goran-mahovlic/ulx3s-extensions/pic/GPDI_Back.png

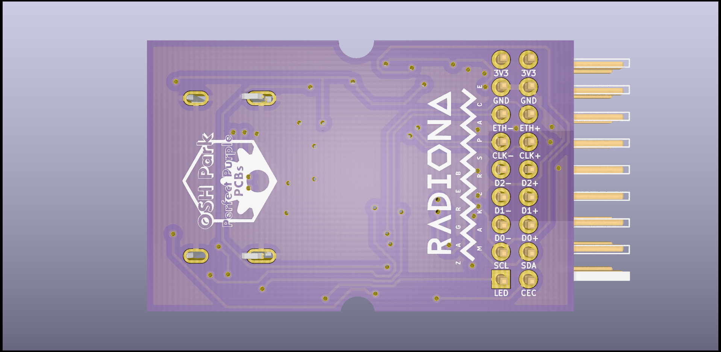
pic/GPDI_Back.png
