goran-mahovlic/ulx3s-extensions/pic/GPDI_INPUT.png

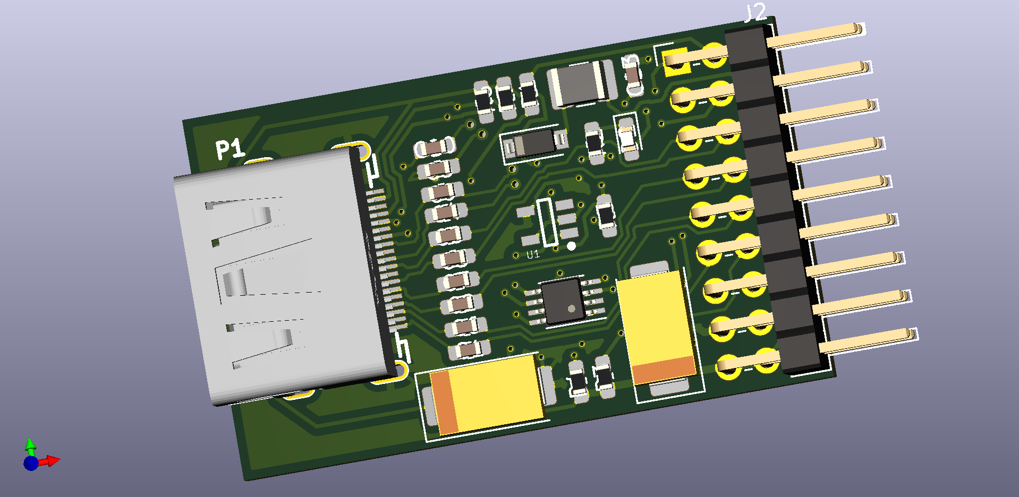
pic/GPDI_INPUT.png
