goran-mahovlic/ulx3s-extensions/pic/GPDI_ULX3S_PMOD_panel.png

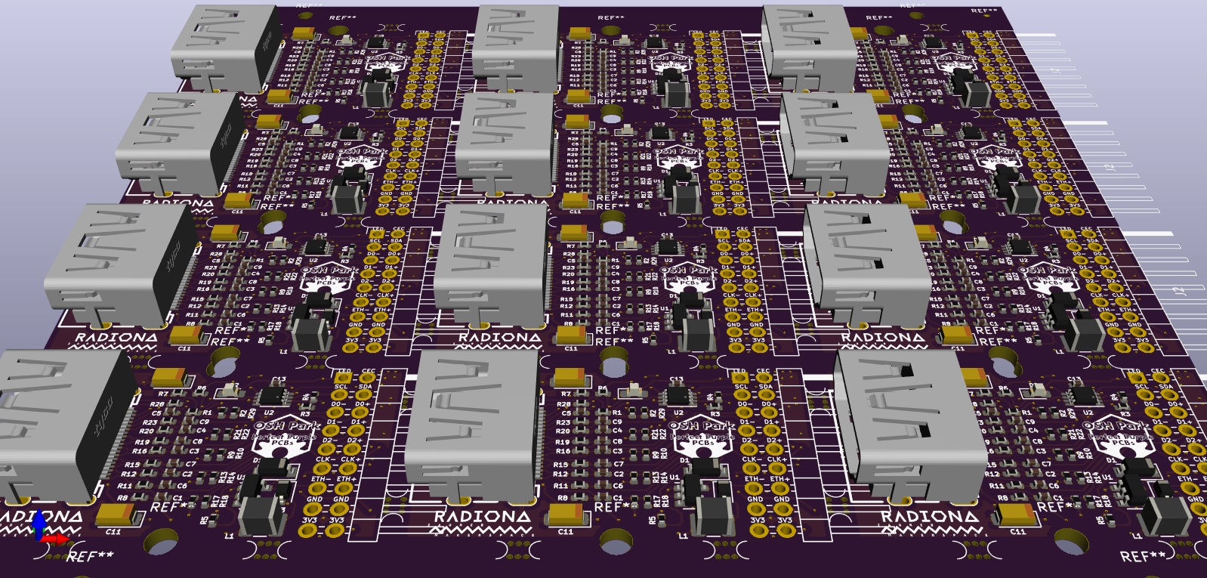
pic/GPDI_ULX3S_PMOD_panel.png
