goran-mahovlic/ulx3s-extensions/pic/midi_pins.png

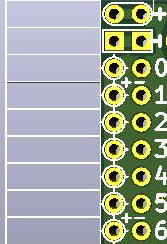
pic/midi_pins.png
