goran-mahovlic/ulx3s-extensions/pic/Shuttleworth Funded.jpg

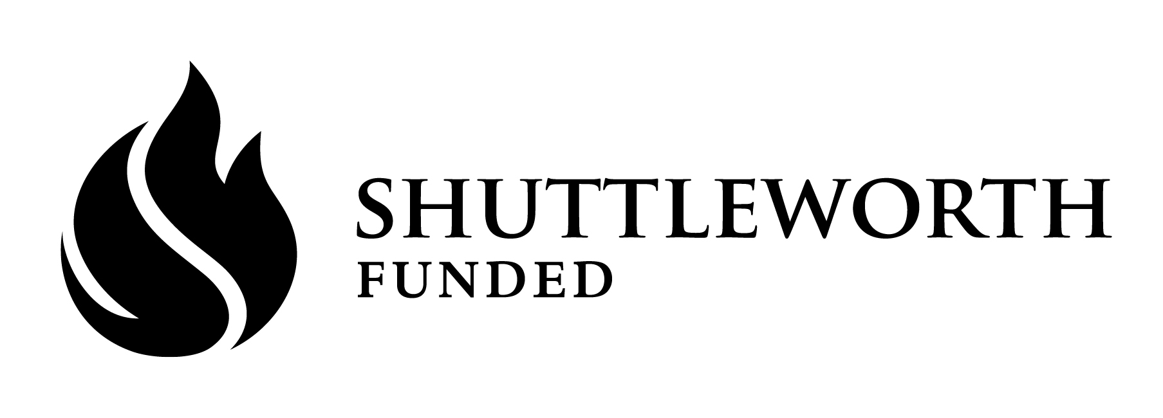
pic/Shuttleworth Funded.jpg
